AlexVT100/ModbusPressureSensor/firmware/include/bitmaps.h

#define BITMAP_W 21
#define BITMAP_H 21

// 'bitmap-fault', 21x21px
const unsigned char bitmap_fault [] PROGMEM = {
	0xff, 0xff, 0xf8, 0xff, 0xff, 0xf8, 0xff, 0xff, 0xf8, 0xf3, 0xfe, 0x78, 0xe1, 0xfc, 0x38, 0xe0, 
	0xf8, 0x38, 0xf0, 0x70, 0x78, 0xf8, 0x20, 0xf8, 0xfc, 0x01, 0xf8, 0xfe, 0x03, 0xf8, 0xff, 0x07, 
	0xf8, 0xfe, 0x03, 0xf8, 0xfc, 0x01, 0xf8, 0xf8, 0x20, 0xf8, 0xf0, 0x70, 0x78, 0xe0, 0xf8, 0x38, 
	0xe1, 0xfc, 0x38, 0xf3, 0xfe, 0x78, 0xff, 0xff, 0xf8, 0xff, 0xff, 0xf8, 0xff, 0xff, 0xf8
};
// 'bitmap-high', 21x21px
const unsigned char bitmap_high [] PROGMEM = {
	0xff, 0xff, 0xf8, 0xff, 0xff, 0xf8, 0xff, 0xdf, 0xf8, 0xff, 0x8f, 0xf8, 0xff, 0x07, 0xf8, 0xfe, 
	0x03, 0xf8, 0xfc, 0x01, 0xf8, 0xf8, 0x00, 0xf8, 0xf0, 0x00, 0x78, 0xe0, 0x00, 0x38, 0xc0, 0x00, 
	0x18, 0xff, 0x07, 0xf8, 0xff, 0x07, 0xf8, 0xff, 0x07, 0xf8, 0xff, 0x07, 0xf8, 0xff, 0x07, 0xf8, 
	0xff, 0x07, 0xf8, 0xff, 0xff, 0xf8, 0xff, 0xff, 0xf8, 0xff, 0xff, 0xf8, 0xff, 0xff, 0xf8
};
// 'bitmap-low', 21x21px
const unsigned char bitmap_low [] PROGMEM = {
	0xff, 0xff, 0xf8, 0xff, 0xff, 0xf8, 0xff, 0xff, 0xf8, 0xff, 0xff, 0xf8, 0xff, 0x07, 0xf8, 0xff, 
	0x07, 0xf8, 0xff, 0x07, 0xf8, 0xff, 0x07, 0xf8, 0xff, 0x07, 0xf8, 0xff, 0x07, 0xf8, 0xc0, 0x00, 
	0x18, 0xe0, 0x00, 0x38, 0xf0, 0x00, 0x78, 0xf8, 0x00, 0xf8, 0xfc, 0x01, 0xf8, 0xfe, 0x03, 0xf8, 
	0xff, 0x07, 0xf8, 0xff, 0x8f, 0xf8, 0xff, 0xdf, 0xf8, 0xff, 0xff, 0xf8, 0xff, 0xff, 0xf8
};
// 'bitmap-none', 21x21px
const unsigned char bitmap_none [] PROGMEM = {
	0x00, 0x00, 0x00, 0x00, 0x00, 0x00, 0x00, 0x00, 0x00, 0x00, 0x00, 0x00, 0x00, 0x00, 0x00, 0x00, 
	0x00, 0x00, 0x00, 0x00, 0x00, 0x00, 0x00, 0x00, 0x00, 0x00, 0x00, 0x00, 0x00, 0x00, 0x00, 0x00, 
	0x00, 0x00, 0x00, 0x00, 0x00, 0x00, 0x00, 0x00, 0x00, 0x00, 0x00, 0x00, 0x00, 0x00, 0x00, 0x00, 
	0x00, 0x00, 0x00, 0x00, 0x00, 0x00, 0x00, 0x00, 0x00, 0x00, 0x00, 0x00, 0x00, 0x00, 0x00
};
